karlp/karlnet/common/kpacket.py

# Karl Palsson, 2010

import struct

import logging

import curve

class human_packet(object):
    """
    Defines the human post processed packet.
    Something that client applications would use
    """
    def __init__(self, node, sensors):
        """Make a human packet from some basic data
        
        :param node: The nodeid this sensor data is from.
        :param sensors: A list of sensor objects
        """
        self.node = node
        self.sensors = sensors
        self.version = 1

        # TODO, this only handles version 1 packets? (fine for sending out from xbees?)

    def wire_format(self):
        frame = struct.pack("> bb", ord('x'),
            (self.version << 4) | len(self.sensors) & 0x0f)
        for s in self.sensors:
            frame += struct.pack("> BI", s.type, s.rawValue)
        return frame

    def __str__(self):
        return "human_packet[node=%#x, sensors=%s]" % (self.node, self.sensors)

class wire_packet(object):
    """
    Defines the packet format used in my sensor network, and handles
    decoding it from an xbee frame
    """
    log = logging.getLogger("WirePacket")
    def __init__(self, arg):
        if len(arg) == 0:
            raise BadPacketException("Packet contains no data!")
        if arg[0] != ord('x'):
            raise BadPacketException("this isn't a kpacket: %s" % arg[0])
        if len(arg) == 11:
            # Handle original packet format here?!!!
            self.log.warn("Handling legacy packet format!")
            self.sensors = []
            self.sensors.append(Sensor(binary=arg[1:6]))
            self.sensors.append(Sensor(binary=arg[6:11]))
            return

        version_samples = arg[1]
        version = version_samples >> 4
        if version == 1 or version == 2:
            num_samples = version_samples & 0xf
            # only real sensors reported?
            if len(arg) != 2 + (num_samples * 5):
                # or the packet is padded to MAX_SENSORS ?
                if len(arg) != 2 + (4 * 5):
                    raise BadPacketException("this is not the right length for a kpacket! %d" % len(arg))
            self.log.debug("handling packet version: %d with %d samples", version, num_samples)
            self.sensors = []
            for i in range (0, num_samples):
                self.sensors.append(Sensor(binary=arg[2 + (i * 5):7 + (i * 5)], version=version))
        else:
            raise BadPacketException("currently only know how to handle version 1 packets, not %d" % version)


class wire_receiver(object):

    log = logging.getLogger("WireReceiver")
    def find_raw_packet(self, serial):
        """
        Try to reliably find and decode one single packet from the serial port
        Rejects invalid lengths.
        Call this in a loop until you get a packet back, rather than None

        Shamelessly ripped from xbee.py, and needs to be put somewhere better,
        like maybe kpacket.py
        """
        self.log.debug("Starting to look for a packet")
        char = serial.read()
        if not char:
            self.log.debug("SERIAL READ TIMEOUT")
            return None

        data = None
        if char == 'x':
            # note, no guarantee that these are good packets!
            version_and_sensorCount = ord(serial.read())
            version = version_and_sensorCount >> 4
            self.log.debug("Appears to be version: %#x", version)
            sensorCount = version_and_sensorCount & 0x0f
            self.log.debug("Sensor count: %d", sensorCount)
            # This is some fugly shit to make it look the same as the xbee wire packets
            buf = []
            buf.append(ord('x'))
            buf.append(version_and_sensorCount)
            # xbees are big endian, but avrs are little endian, so raw received
            # packets have longs in reversed byte ordering.
            for i in range (0, sensorCount):
                buf.append(ord(serial.read()))
                sensor = struct.unpack("< L", serial.read(4))[0]
                buf.append(sensor >> 24)
                buf.append((sensor & 0x00ff0000) >> 16)
                buf.append((sensor & 0x0000ff00) >> 8)
                buf.append(sensor & 0xff)
            self.log.debug("data = %s", buf)
            return buf
        else:
            self.log.debug("Found instead: %#x", ord(char))
            return None

class Sensor(object):
    """
    Defines an individual sensor reading, made up of a type, and a raw value
    """
    log = logging.getLogger("Sensors")
    def __init__(self, binary=None, type=None, raw=None, value=None, version=1):
        """If binary, then decode binary as raw sensor bytes.
        Otherwise, just make an object like we're told"""
        if binary:
            self.__decodeBinary(binary, version)
        else:
            self.type = type
            self.rawValue = raw
            self.value = value

        if value is None and self.rawValue is not None:
            (self.value, self.units) = self.__decode()

    def __decodeBinary(self, arg, version):
        """Internal method for decoding raw binary data from a wire_packet"""
        if len(arg) != 5:
            raise BadPacketException("sensor readings should be 5 bytes! 5!=%d" % len(arg))
        self.log.debug("Decoding bytes into a sensor object (ver:%d): *%s*", version, arg)
        self.type = arg[0]
        if version == 1:
            self.rawValue = (arg[1] << 24) + (arg[2] << 16) + (arg[3] << 8) + arg[4]
        if version == 2:
            self.rawValue = (arg[4] << 24) + (arg[3] << 16) + (arg[2] << 8) + arg[1]
        (self.value, self.units) = self.__decode()

    
    def __convertSensor_LM35(self, rawValue, reference):
        rawNum = float(rawValue)
        milliVolts = rawNum / 1024 * reference
        tempC = milliVolts / 10
        return tempC

    def __convertSensor_TMP36(self, rawValue, reference):
        rawNum = float(rawValue)
        milliVolts = rawNum / 1024 * reference
        lessOffset = (milliVolts - 750) / 10
        tempC = 25 + lessOffset
        return tempC

    def __convertNTC_10K_3V3(self, rawValue, bits=10):
            vout = float(rawValue) / (2**bits - 1) * 3.3
            r1_r2 = vout/(3.3-vout)
            ntc = r1_r2 * 10000
            cc = curve.curve("ntc.10kz.curve.csv")
            return (cc.find_temp(ntc), 'degreesCelsius')
        
    def __decode(self):
        """
        decode the raw sensor value
    type is the sensor type id, known values are...
     chr(36) for tmp-36 vs a 2.56 vref
     chr(37) for tmp-36 vs a 1.1 vref
     'i' for tiny85 internal temp sensor reading, raw  (measures against 1.1vref)
     'I' for mega32u4 internal temp sensor (measures against 2.56vref)
     'f' for raw frequency measurements from HCH1000 humidity sensor
        """
        self.log.debug("Decoding type:%s, raw=%s", self.type, self.rawValue)
        if self.type == 35:
            return (self.__convertSensor_LM35(self.rawValue, 2560), 'degreesCelsius')
        if self.type == 36:
            return (self.__convertSensor_TMP36(self.rawValue, 2560), 'degreesCelsius')
        if self.type == 37:
            return (self.__convertSensor_TMP36(self.rawValue, 1100), 'degreesCelsius')
        if self.type == 38: # KPS_SENSOR_TEMPERATURE
            return (self.rawValue / 1000.0, 'degreesCelsius')
        if self.type == 39: # KPS_SENSOR_HUMIDITY
            return (self.rawValue / 1000.0, 'percentRH')
        if self.type == 40:
            return (self.__convertNTC_10K_3V3(self.rawValue, 12))
        if self.type == ord('f'):
            # 555 timer is C = 1/f / 300k / 0.693 (555 constant)
            # seems to range from about 400pf (very dry) to about 1100pf (quite humid)
            if (self.rawValue == 0):
                return (0, 'uninitialised counter');
            return ((1e12 / (self.rawValue * 300000 * 0.693)), 'picoFarads')
        # need calibration!
        if self.type == ord('i'):
            return (self.rawValue  - 273, 'degreesCelsius')
        if self.type == ord('I'):
            return (self.rawValue - 273, 'degreesCelsius')
        if self.type == ord('a'):
            return (self.__convertNTC_10K_3V3(self.rawValue))
        if self.type == ord('b'):
            return (self.rawValue, 'boolean')
        if self.type == ord('z'):
            return (self.rawValue, 'sensor test value')
        self.log.warn("Unknown sensor type: %s", self.type)
        return (0, "na")


    def __repr__(self):
        return ("sensor[t:%d, raw=%d(%#x), val=%f]" %
            (self.type, self.rawValue, self.rawValue, self.value))
        

class BadPacketException(Exception):
    """thrown when you attempt to create a kpacket from an illegal rx frame"""
    def __init__(self, msg):
        self.msg = msg
