karlp/karlnet/nodes/boxcar/firmware/ms_systick.h

/* 
 * Karl Palsson <karlp@tweak.net.au> 2012
 */

#ifndef MS_SYSTICK_H
#define	MS_SYSTICK_H

#ifdef	__cplusplus
extern "C" {
#endif

#include <stdio.h>
    
int64_t millis(void);
void delay_ms(int ms);



#ifdef	__cplusplus
}
#endif

#endif	/* MS_SYSTICK_H */
